PlayingWithFusion/SnakeEyesDocs/img/render_1.jpg

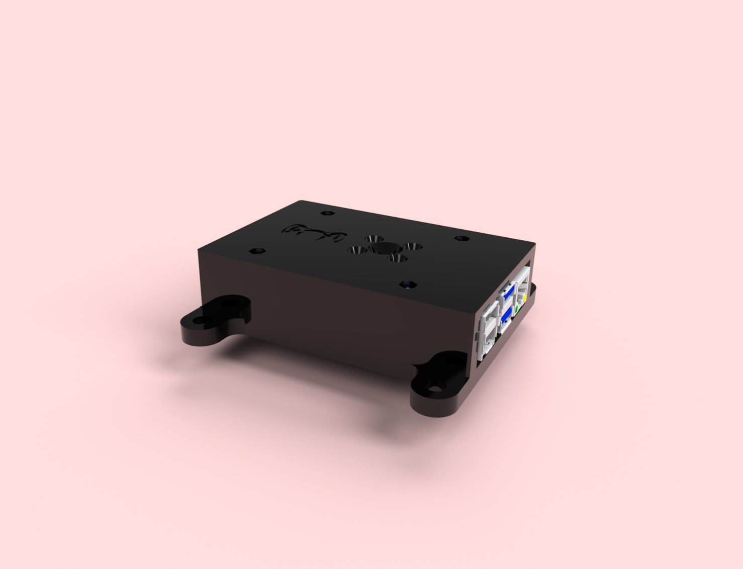
img/render_1.jpg
