PlayingWithFusion/SnakeEyesDocs/img/render_2.jpg

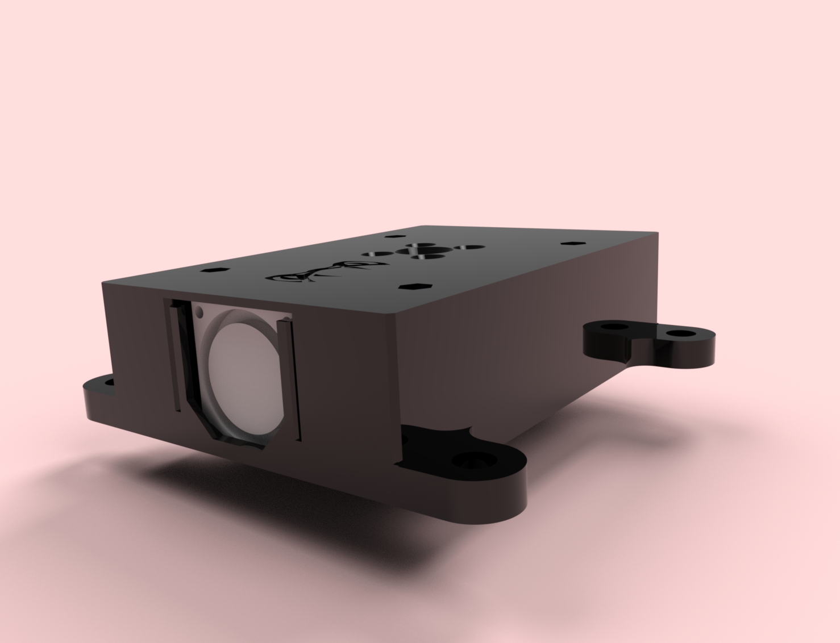
img/render_2.jpg
