PlayingWithFusion/SnakeEyesDocs/img/render_3.jpg

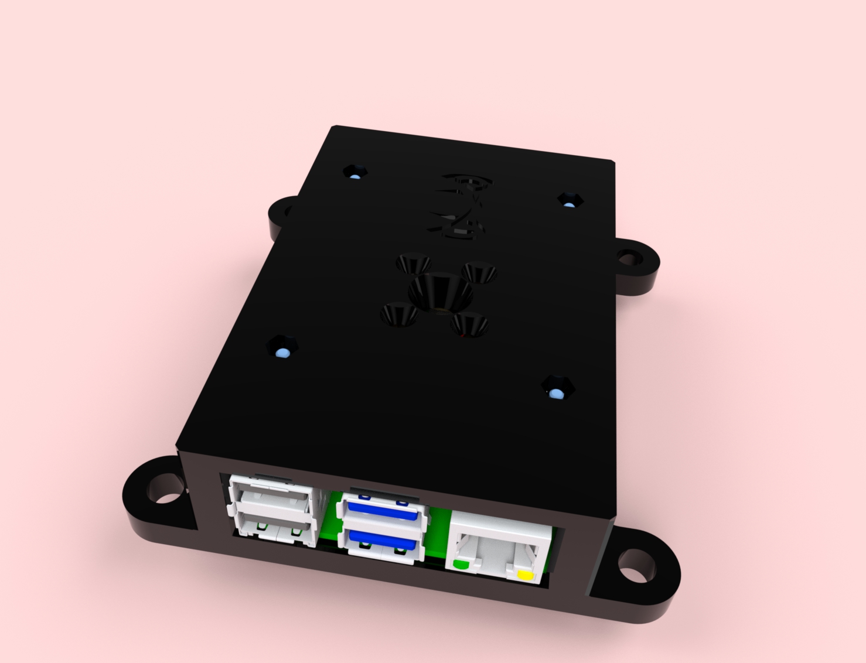
img/render_3.jpg
