PlayingWithFusion/SnakeEyesDocs/img/render_5.jpg

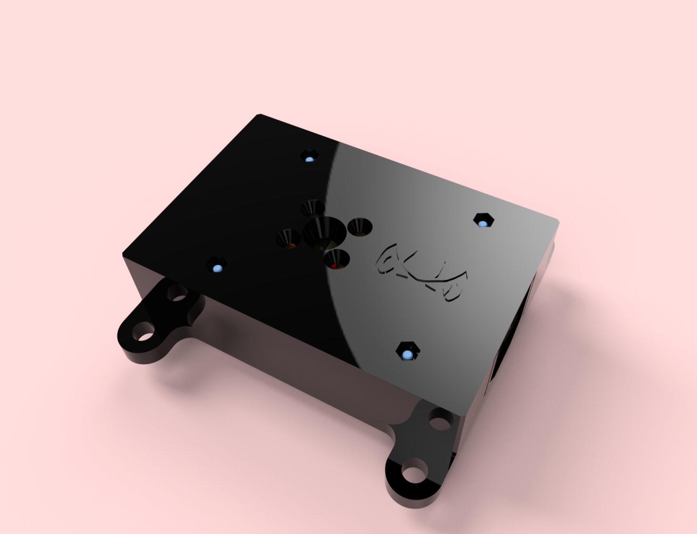
img/render_5.jpg
