PlayingWithFusion/SnakeEyesDocs/img/render_8.jpg

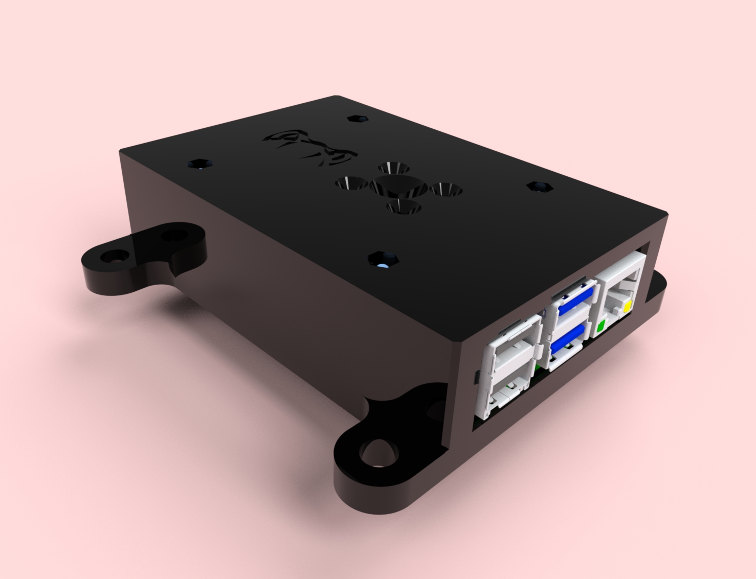
img/render_8.jpg
